daveythacher/LED_Matrix_RP2040/LED_Matrix/main.cpp

/* 
 * File:   main.cpp
 * Author: David Thacher
 * License: GPL 3.0
 */
 #include "pico/stdlib.h"

extern void matrix_start();
extern void serial_start();
extern void isr_start();
extern void loop();

int main() {
    matrix_start();
    serial_start();
    isr_start();
    loop();
}
